vpolda/Snake-Tank/Hardware/graphics/snake_filled.bmp

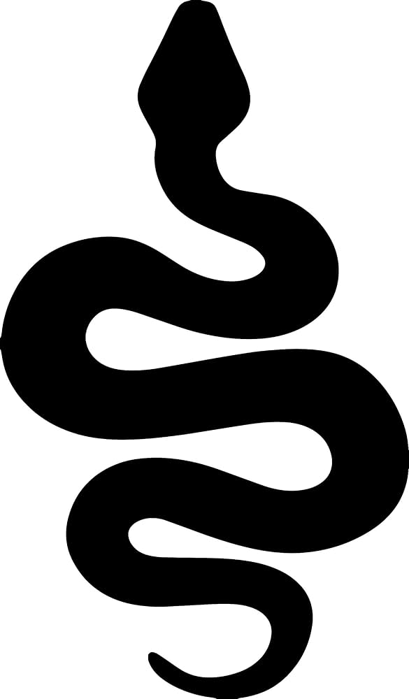
Hardware/graphics/snake_filled.bmp
